arcnode-io/edp-interface-plates/output/drawings/CG.dxf

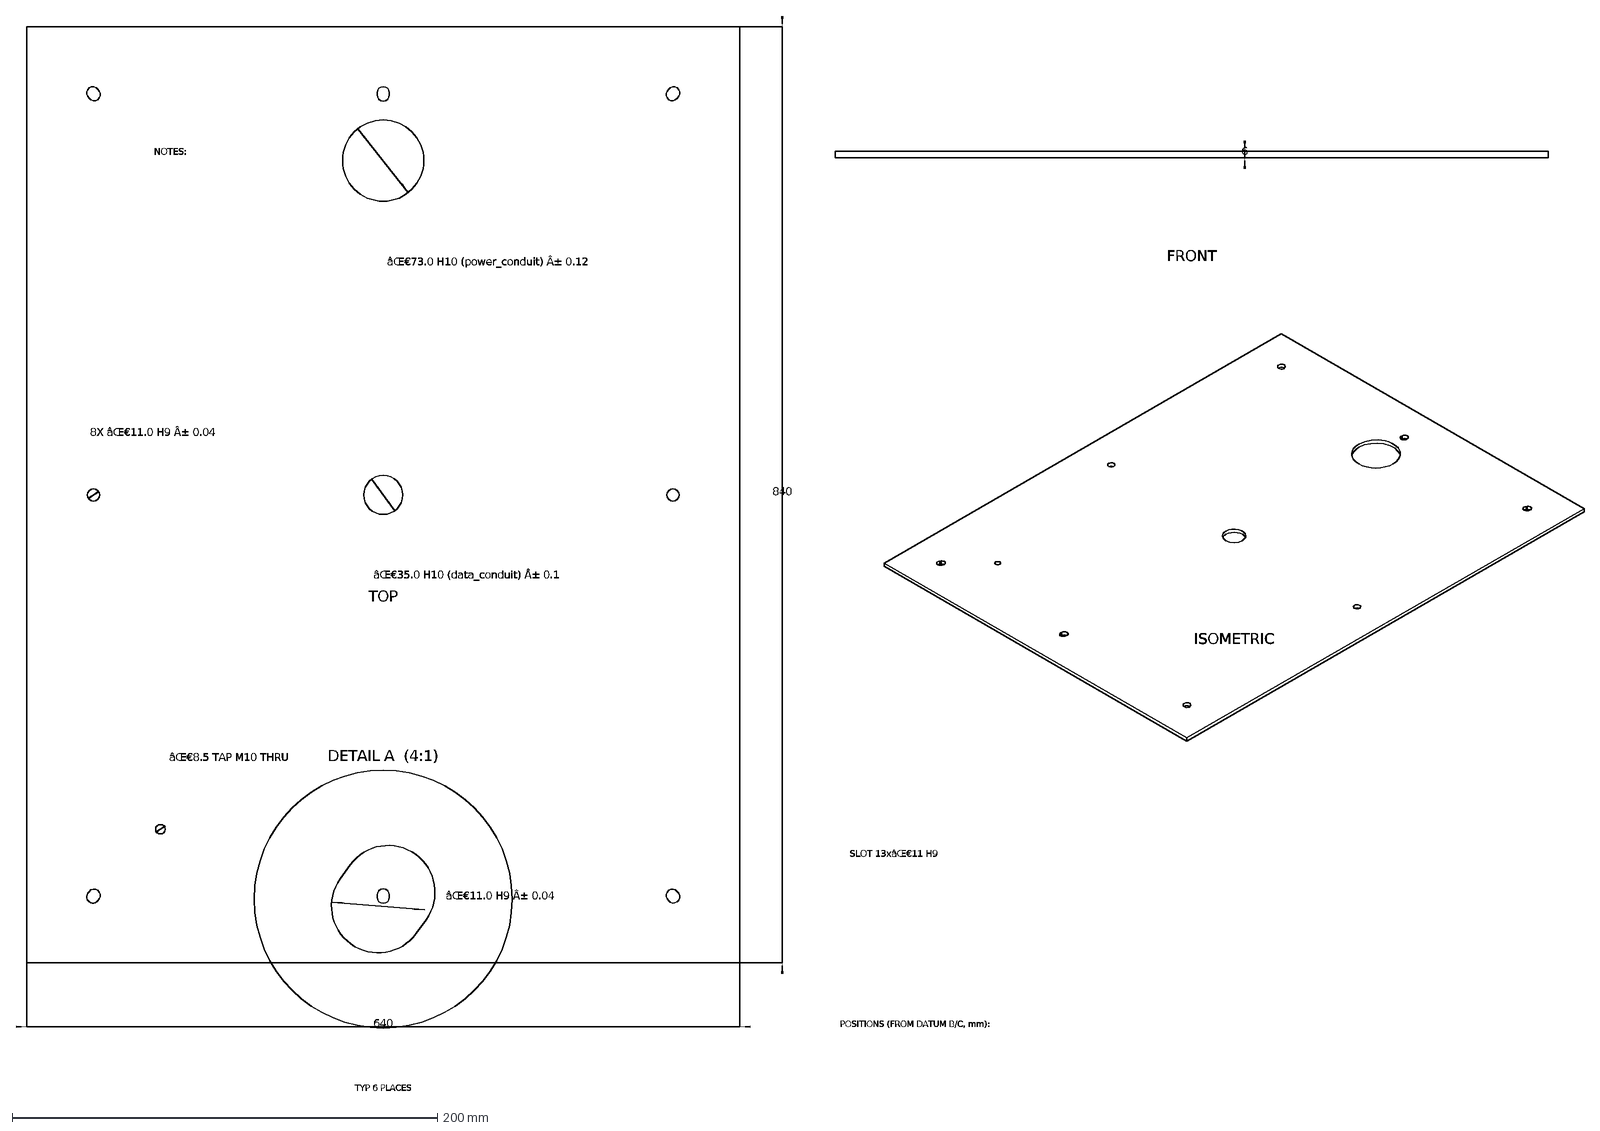
[picture p11: CAD file, 2026-05-10]
output/drawings/CG.dxf
640
840
âŒ€73.0 H10 (power_conduit) Â± 0.12
âŒ€35.0 H10 (data_conduit) Â± 0.1
âŒ€8.5 TAP M10 THRU
8X âŒ€11.0 H9 Â± 0.04
POSITIONS (FROM DATUM B/C, mm):
SLOT 13xâŒ€11 H9
6
âŒ€11.0 H9 Â± 0.04
TYP 6 PLACES
DETAIL A (4:1)
NOTES:
TOP
FRONT
ISOMETRIC
